RSiderits/Rack_Carry/IMG_2274.JPG

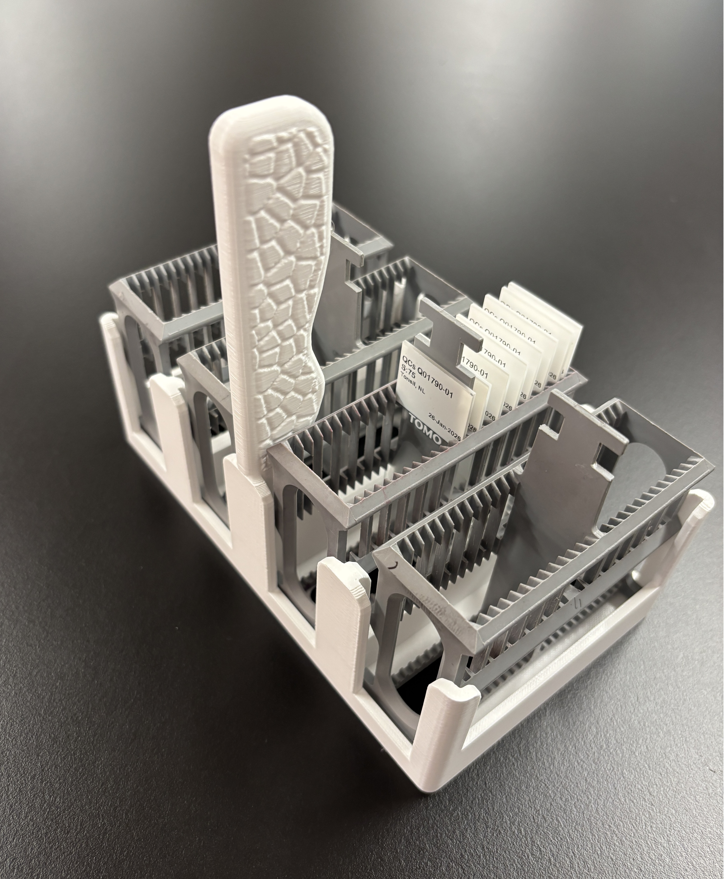
IMG_2274.JPG
