RSiderits/Rack_Carry/IMG_2278.JPG

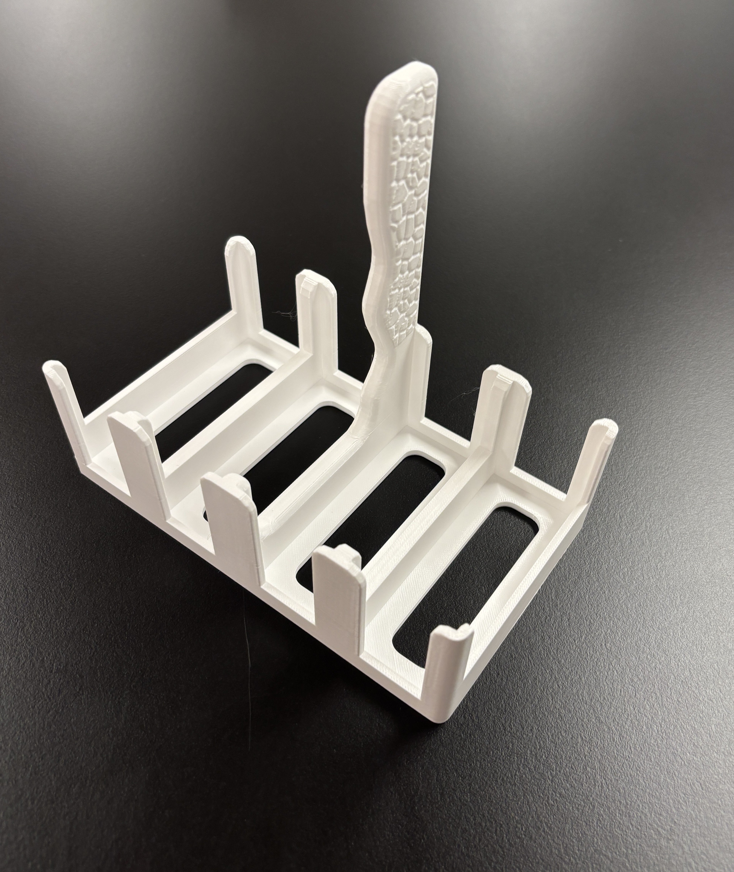
IMG_2278.JPG
