RSiderits/Rack_Carry/IMG_2312.JPG

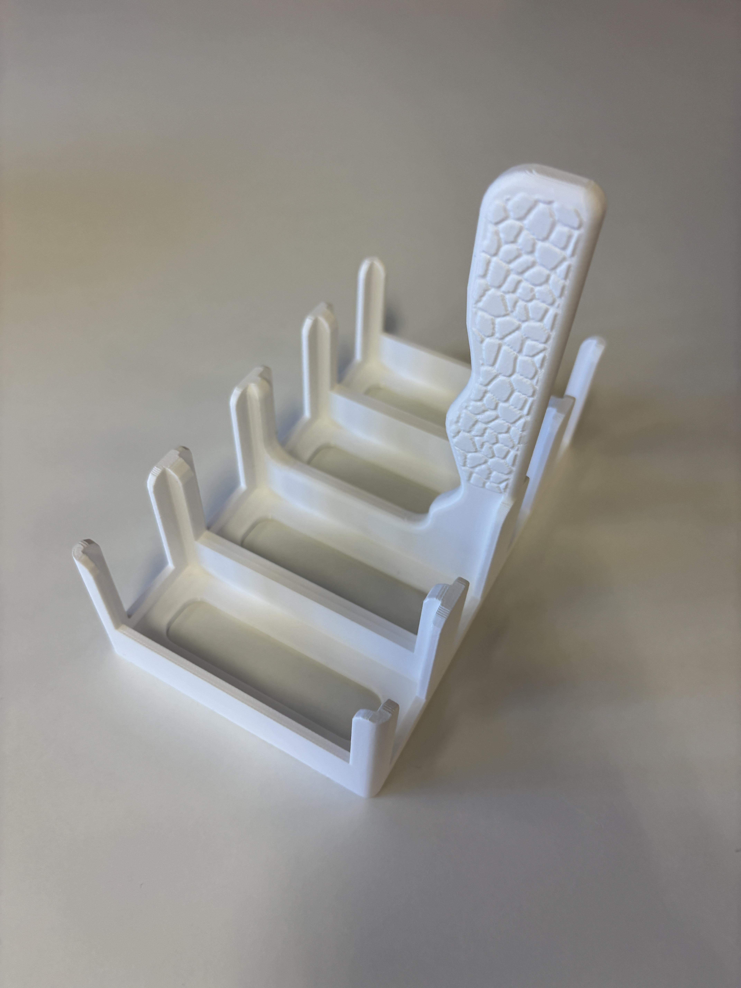
IMG_2312.JPG
