RSiderits/Rack_Carry/IMG_2314.JPG

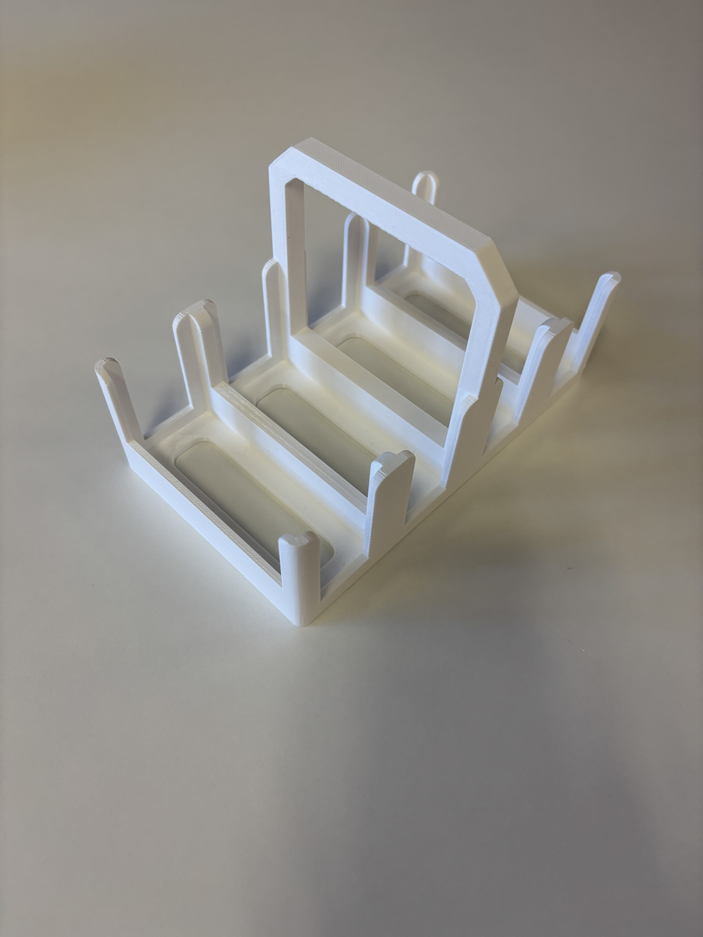
IMG_2314.JPG
